vu2cpl/esp32-winkeyer/src/web.cpp

// ============================================================
//  VUKEYER — settings web server
//
//  Synchronous WebServer on port 80. Serviced from loop(), never
//  from the keyer task: serving the page takes a few ms of socket
//  work and element timing must not see it.
//
//  Routes:
//    GET  /              the settings console (one static page)
//    GET  /api/state     everything the page renders, as JSON
//    POST /api/set?k=..&v=..   one setting, via Settings::apply()
//    POST /api/send?t=..       queue text as CW
//    POST /api/tune?v=on|off   key down for tuning
//    GET  /api/flextrace       recent lines to/from the radio (?clear=1)
//    GET  /api/cwtable         radio CW timing per WPM; POST ?reset=1 forgets it
//    GET  /api/bt              Bluetooth keyboard detail + scan list
//    POST /api/bt?scan=1 | connect=<addr>&type=<n> | forget=1 | restart=1
//
//  Deliberately no authentication: this is shack-LAN kit on a
//  trusted VLAN, same posture as the WinKeyer TCP port next to it.
// ============================================================

#include "web.h"
#include "log.h"
#include "config.h"
#include "settings.h"
#include "keyer.h"
#include "fsk.h"
#include "memories.h"
#include "hostlink.h"
#include "flex.h"
#include "bt.h"
#include <WebServer.h>
#include <ESPmDNS.h>
#include <ArduinoJson.h>
#include <WiFi.h>

namespace {

WebServer server(80);
bool started = false;

// Styled after soft-MORCONI's console: dark chassis, amber panel labels,
// LED-style status dots. Fonts are system stacks, not Google Fonts — the
// keyer is often on a VLAN with no route to the internet, and a page that
// waits on fonts.googleapis.com would stall for every operator.
const char PAGE[] PROGMEM = R"HTML(<!DOCTYPE html>
<html lang="en"><head><meta charset="utf-8">
<meta name="viewport" content="width=device-width,initial-scale=1">
<title>VUKEYER — Settings</title><style>
:root{--chassis:#2d2d30;--dark:#1a1a1c;--bezel:#0a0a0b;--label:#d8cfb8;
--dim:#8a8275;--amber:#ffaa22;--green:#2aff5a;--red:#ff2a1a;--off:#3a1a18}
*{box-sizing:border-box}
body{margin:0;padding:8px;background:#0c0c0e radial-gradient(ellipse at top,#1a1a1c,#050505);
color:var(--label);font:14px/1.45 ui-monospace,Menlo,Consolas,monospace;min-height:100vh}
/* Panels tile into as many columns as the window allows, so the whole
   console fits one screen on a desktop and falls back to a single column
   on a phone. auto-fit + minmax does that without a breakpoint per size. */
.rig{max-width:1500px;margin:0 auto;padding:10px;border-radius:12px;
display:grid;grid-template-columns:1fr;
gap:6px 12px;align-items:start;
background:linear-gradient(180deg,#4a4a50 0%,#2d2d30 30%,#1f1f22 100%);
box-shadow:inset 0 2px 0 rgba(255,255,255,.18),inset 0 -3px 0 rgba(0,0,0,.7),0 24px 48px rgba(0,0,0,.7)}
/* Full-width furniture: the header, the lamps, a warning, the big speed
   readout and the footer read across the whole console, not per column. */
.rig>.brand,.rig>.leds,.rig>.slicewarn,.rig>.speed,.rig>.foot{grid-column:1/-1}
/* The backend panel carries the most rows; give it two columns when there
   is room, and let it collapse with everything else when there is not. */
/* Explicit breakpoints rather than auto-fit: auto-fit kept a ~800px window
   in ONE column, which stretched every slider across the full width and
   squeezed the memories into a single inner cell. */
@media(min-width:760px) {.rig{grid-template-columns:repeat(2,minmax(0,1fr))}}
@media(min-width:1150px){.rig{grid-template-columns:repeat(3,minmax(0,1fr))}}
@media(min-width:1680px){.rig{grid-template-columns:repeat(4,minmax(0,1fr))}}
@media(min-width:1150px){
  .wide{grid-column:span 2}
  /* BACKEND needs two columns; let a later card fill the hole it leaves. */
  .rig{grid-auto-flow:row dense}
  /* Lamps and the speed readout share one line instead of taking two. */
  .rig>.leds{grid-column:1/-2}
  .rig>.speed{grid-column:-2/-1;margin-bottom:0}
}
/* A slider does not get more useful past a few hundred pixels; without a
   cap a full-width card turns Speed into a metre of travel. */
input[type=range]{max-width:340px}
/* Memories and the backend panel share a grid row, as do USB / WIFI and
   FSK / RTTY below them; each pair is stretched to one height.
   Memories shares a grid row with the backend panel, which is much taller.
   .rig is align-items:start, so the card stopped at its content and the two
   ended at different heights. */
.stretch{align-self:stretch}
/* Every panel ends level with the ones it shares a row with. */
.rig>fieldset{align-self:stretch}
/* The six memories are wrapped in one div, so they were living in a single
   inner column. Give that div the full card and tile inside it. */
#mems{grid-column:1/-1;display:grid;
grid-template-columns:repeat(auto-fit,minmax(290px,1fr));gap:2px 12px}
.brand{display:flex;justify-content:space-between;align-items:baseline;
padding-bottom:8px;border-bottom:2px solid var(--bezel);margin-bottom:4px}
.brand b{font-size:19px;letter-spacing:3px;color:var(--amber);text-shadow:0 0 12px rgba(255,170,34,.5)}
.brand span{font-size:11px;color:var(--dim)}
/* no display rule here, so the hidden attribute still hides it */
.slicewarn{padding:9px 12px;margin:-6px 0 14px;border-radius:8px;font-size:13px;
background:rgba(255,170,34,.12);border:1px solid var(--amber);color:var(--amber)}
.leds{display:flex;gap:14px;flex-wrap:wrap;padding:8px 12px;margin-bottom:2px;
background:var(--bezel);border-radius:8px;font-size:11px;letter-spacing:1px}
.led{display:flex;align-items:center;gap:6px;color:var(--dim)}
.led i{width:9px;height:9px;border-radius:50%;background:var(--off);display:inline-block}
.led.on i{background:var(--green);box-shadow:0 0 8px var(--green)}
.led.warn i{background:var(--amber);box-shadow:0 0 8px var(--amber)}
.speed{background:var(--bezel);border-radius:8px;padding:8px 16px;margin-bottom:2px;
display:flex;align-items:baseline;gap:12px}
.speed b{font-size:34px;color:var(--amber);text-shadow:0 0 16px rgba(255,170,34,.45);line-height:1}
.speed span{color:var(--dim);font-size:12px;letter-spacing:2px}
fieldset{border:1px solid #44444a;border-radius:8px;margin:0;padding:6px 12px 9px;
min-width:0}   /* min-width:0 or a long row stretches its grid column */
/* Rows tile inside a panel too — a label plus one control is ~230px, so
   two or three sit side by side in a wide panel instead of stacking. */
fieldset{display:grid;grid-template-columns:repeat(auto-fit,minmax(196px,1fr));
gap:2px 14px;align-content:start}
fieldset>legend{grid-column:1/-1}
/* A merged card keeps its old panels as sections under a small heading. */
.sub{grid-column:1/-1;margin:8px 0 0;padding-top:6px;border-top:1px dashed #44444a;
color:var(--amber);font-size:10px;letter-spacing:2px;opacity:.8}
.sub.first{margin-top:0;padding-top:0;border-top:0}
.sub[title]{cursor:help}
/* Anything with a slider, a free-text field or its own buttons wants the
   full width of its panel; :has covers the sliders without marking each. */
.row.full,.row:has(input[type=range]),.row:has(input[type=text]):not(.mem){grid-column:1/-1}

legend{color:var(--amber);font-size:11px;letter-spacing:2px;padding:0 6px}
.row{display:flex;align-items:center;gap:9px;margin:4px 0;flex-wrap:wrap}
/* An author rule beats the hidden attribute's default display:none, so
   .row{display:flex} kept "hidden" rows on screen. */
.row[hidden]{display:none!important}
/* Closed, it is one tile beside Radio and Keying; open, it takes the width. */
details.adv{margin:4px 0;align-self:center}
details.adv[open]{grid-column:1/-1;margin-top:6px;border-top:1px dashed #44444a;padding-top:4px}
details.adv[hidden]{display:none!important}
details.adv summary{cursor:pointer;color:var(--dim);font-size:12px}
.advwarn{margin:6px 0;padding:6px 9px;border-radius:6px;font-size:12px;
background:rgba(255,170,34,.12);border:1px solid var(--amber);color:var(--amber)}
.row label{flex:0 0 92px;color:var(--dim);font-size:12px}
input,select,button{font:inherit;background:#131315;color:var(--label);
border:1px solid #44444a;border-radius:5px;padding:3px 8px;font-size:13px}
input[type=range]{flex:1;min-width:150px;padding:0;border:none;background:none;
-webkit-appearance:none;appearance:none;height:18px}
input[type=range]::-webkit-slider-runnable-track{height:5px;border-radius:3px;
background:#131315;box-shadow:inset 0 1px 2px rgba(0,0,0,.9)}
input[type=range]::-moz-range-track{height:5px;border-radius:3px;background:#131315}
input[type=range]::-webkit-slider-thumb{-webkit-appearance:none;appearance:none;
width:15px;height:15px;margin-top:-5px;border-radius:50%;border:1px solid #1a1a1c;
background:linear-gradient(180deg,#d8cfb8,#8a8275);box-shadow:0 0 7px rgba(255,170,34,.55)}
input[type=range]::-moz-range-thumb{width:15px;height:15px;border-radius:50%;
border:1px solid #1a1a1c;background:linear-gradient(180deg,#d8cfb8,#8a8275)}
input[type=checkbox]{accent-color:var(--amber)}
input[type=text]{width:92px}
/* Wide enough for "2000" and the spinner, narrow enough that label + field
   + unit clears a half-width panel column with room to spare. */
input[type=number]{width:78px}
button{cursor:pointer;background:linear-gradient(180deg,#44444a,#26262a);
letter-spacing:.5px;padding:3px 9px;font-size:12px}
button:hover{border-color:var(--amber);color:var(--amber)}
button.hot{color:var(--red);border-color:#5a2420}
.val{color:var(--amber);min-width:56px;font-size:13px}
/* A fixed unit ("ms", "WPM") is not a readout: reserving 56px for it was
   enough to push it onto a second line inside a half-width panel column.
   .val keeps its width because a CHANGING value there would resize the
   slider beside it on every drag. */
.unit{color:var(--amber);font-size:13px;white-space:nowrap}
/* A <select> is as wide as its longest option and will not shrink below
   it, so "1200 8N2 - ... standard" hung out past the panel border. */
select{max-width:100%}
/* Memories: six rows that must each stay on ONE line, or the panel becomes
   the tallest thing on the page and nothing else fits beside it. */
.row.mem{margin:3px 0;gap:6px}
.row.mem button{padding:4px 7px;font-size:11px;letter-spacing:0}
.row label[title]{border-bottom:1px dotted var(--dim);cursor:help}
legend[title]{cursor:help}
#msg{min-height:16px;font-size:12px;color:var(--green);margin-top:4px}
#msg.err{color:var(--red)}
.foot{margin-top:4px;font-size:11px;color:var(--dim);text-align:center}
</style></head><body><div class="rig">
<div class="brand"><b>VUKEYER</b><span>VU2CPL &middot; ESP32</span></div>

<div class="leds">
<div class="led" id="l-host"><i></i>HOST</div>
<div class="led" id="l-tcp"><i></i>TCP</div>
<div class="led" id="l-key"><i></i>KEY</div>
<div class="led" id="l-tune"><i></i>TUNE</div>
<div class="led" id="l-pot"><i></i>POT</div>
<div class="led" id="l-flex"><i></i>FLEX</div>
<div class="led" id="l-disp"><i></i>OLED</div>
<div class="led" id="l-kbd"><i></i>KBD</div>
</div>
<div class="slicewarn" id="slicewarn" hidden></div>
<div class="slicewarn" id="practicewarn" hidden>PRACTICE &mdash; sidetone only, nothing is transmitted</div>

<div class="speed"><b id="wpmBig">--</b><span>WPM</span><span id="src"></span></div>

<fieldset><legend>KEYER</legend>
<div class="row"><label title="Sidetone only: paddle, memories, typed text, a logger's text and TUNE all sound in your ear, but no KEY or PTT line is driven, nothing is sent to the radio, and RTTY is refused. Turning it on or off stops whatever is being sent. Not saved: the keyer always boots ready to transmit.">Practice</label>
  <label style="flex:0 0 auto"><input type="checkbox" id="practice"> sidetone only, no TX</label></div>
<div class="row"><label title="Sending speed in words per minute (PARIS timing: dit = 1200/WPM ms). A logger or the speed pot can override this; only what you set here is saved.">Speed</label>
  <input type="range" id="wpm" min="5" max="60"><span class="val" id="wpmV"></span></div>
<div class="row"><label title="Echo of characters you send on the PADDLE, so a logger can capture hand-sent text. This is mode register bit 6 of the logger protocol, separate from character echo of buffered text. Auto follows what the host asks for — but RUMlogNG sets 0x07 and never requests it, so force it On if you want hand-sent text logged.">Paddle echo</label>
  <select id="pecho"><option value="auto">Auto (follow host)</option>
  <option value="on">On</option><option value="off">Off</option></select>
  <span class="val" id="pechoState"></span></div>
<div class="row"><label title="Iambic A releases both paddles to stop after the current element; iambic B sends one more. Swap exchanges dit and dah if the paddle is wired the other way round.">Mode</label>
  <select id="mode"><option value="a">Iambic A</option><option value="b">Iambic B</option></select>
  <label style="flex:0 0 auto"><input type="checkbox" id="swap"> swap paddles</label></div>
<div class="row"><label title="Monitor tone pitch in Hz, 300-1000, default 600. Local only — it never reaches the air. A logger can ask for another pitch over the host link (the command sends 4000/N); that lasts its session and is clamped to this range.">Sidetone</label>
  <input type="range" id="sthz" min="300" max="1000" step="10"><span class="val" id="sthzV"></span></div>
<div class="sub">TIMING</div>
<div class="row"><label title="Mark/space balance, 10-90, nominal 50. Higher makes elements longer and gaps shorter WITHOUT changing the WPM. Raise it a little if your fist sounds clipped on the air.">Weight</label>
  <input type="range" id="weight" min="10" max="90"><span class="val" id="weightV"></span></div>
<div class="row"><label title="Dah length relative to a dit, 33-66, nominal 50 = the standard 3 dits. Away from 50 the CW stops being standard-weight, so move it only to match a fist you already like.">Dah ratio</label>
  <input type="range" id="ratio" min="33" max="66"><span class="val" id="ratioV"></span></div>
<div class="row"><label title="0 = off. Otherwise characters stay at the Speed above while the GAPS stretch to this slower WPM — the standard way to learn at speed. Must be 0 or 5-60; 1-4 is not a legal value.">Farnsworth</label>
  <input type="number" id="farns" min="0" max="60"><span class="unit">WPM</span></div>
<div class="sub">SPEED POT</div>
<div class="row"><label title="10k linear pot on GPIO34, wiper to the pin, 100nF to GND. Leave this OFF until one is actually wired: the pin floats and noise will drive your speed. The knob overrides a host-set speed the moment you turn it.">Knob</label>
  <label style="flex:0 0 auto"><input type="checkbox" id="pot"> enabled</label></div>
<div class="row full"><label title="WPM at each end of the knob travel. Expect a small dead zone at the top: the ESP32 ADC saturates near 3.1 V rather than 3.3 V.">Range</label>
  <input type="number" id="potmin" min="5" max="59"><span class="unit">to</span>
  <input type="number" id="potmax" min="6" max="60"><span class="unit">WPM</span></div>
<div class="sub" id="legPtt" title="">PTT</div>
<div class="row"><label title="The PTT line itself: GPIO32, and GPIO19 for radio 2. Unticked, PTT is never asserted at all. It stays live on both backends, for an amp or a sequencer.">PTT line</label>
  <label style="flex:0 0 auto"><input type="checkbox" id="ptt"> enabled</label></div>
<div class="row"><label title="Master on/off for the tone in your ear, from the piezo on GPIO4. Off means silence regardless of anything else.">Audio</label>
  <label style="flex:0 0 auto"><input type="checkbox" id="st"> sidetone</label></div>
<div class="row"><label title="Delay in ms between asserting PTT and the first element, so a relay or amp has time to switch. Applies to the local GPIO32 line; the Flex radio does its own T/R.">Lead-in</label>
  <input type="number" id="lead" min="0" max="2000"><span class="unit">ms</span></div>
<div class="row"><label title="How long PTT is held after the last element, in ms. Releases BOTH the local line and, on the Flex backend, the radio. A useful reference: one word gap is 7 dits = 8400/WPM ms, so 400 ms is exactly one word space at 21 WPM.">Tail</label>
  <input type="number" id="tail" min="0" max="2000"><span class="unit">ms</span></div>
</fieldset>

<fieldset><legend title="Six canned messages kept in flash, played through whichever backend is current. %C in the text expands to your callsign, so a memory survives a contest call change. No GPIO cost — front-panel buttons can be wired to these later.">MEMORIES</legend>
<div class="row"><label title="Expands wherever %C appears in a memory.">Callsign</label>
  <input type="text" id="call" style="width:120px" placeholder="VU2CPL"></div>
<div id="mems"></div>
<div class="sub" title="Type text and press Enter or SEND to transmit it. The SEND button turns into STOP while anything is going out — a message, a memory or tune — and ends it, clearing the radio's buffer as well as the keyer's. TUNE keys continuously for tuning an amp. Number boxes on this page step with the arrow keys, Shift for 10.">SEND</div>
<div class="row"><input type="text" id="txt" style="flex:1;width:auto" placeholder="CQ TEST VU2CPL">
  <button id="sendBtn" onclick="sendOrStop()">SEND</button>
  <button id="tuneBtn" onclick="tuneOrStop()">TUNE</button></div>
<div id="msg"></div>
<div class="sub" title="RTTY FSK keying line on GPIO27: Baudot at 45.45 baud, 1 start bit, 5 data bits, 1.5 stop bits, mark when idle. Invert if your rig wants mark low — wrong polarity prints as reversed-case gibberish at the far end rather than silence. Diddle sends LTRS while the transmitter is up with nothing to say, keeping the far end synchronised between overs. PTT is held for the whole over, not per character.">FSK / RTTY</div>
<div class="row"><input type="text" id="fsktxt" style="flex:1;width:auto" placeholder="RYRYRY DE VU2CPL">
  <button id="fskBtn" onclick="fskSendOrStop()">SEND</button></div>
<div class="row full"><label title="45.45 baud is standard amateur RTTY. 75 is used on some commercial circuits.">Baud</label>
  <select id="fskbaud"><option value="45.45">45.45 (standard)</option>
  <option value="50">50</option><option value="75">75</option></select>
  <span class="val" id="fskState"></span></div>
<!-- The two switches get their own row: a label, a select and two checkboxes
     on one line overflow this panel at every window width, and the leftover
     checkbox wrapping alone underneath is the ugliest way to lose that fight.
     The spacer keeps them lined up with the controls above. -->
<div class="row full"><span style="flex:0 0 92px"></span>
  <label style="flex:0 0 auto"><input type="checkbox" id="fskinv"> invert</label>
  <label style="flex:0 0 auto"><input type="checkbox" id="fskdid"> diddle</label></div>
</fieldset>

<fieldset class="wide stretch"><legend>BACKEND</legend>
<div class="row"><label title="Enable the FlexRadio backend: discovery, connection and keying over the network. Harmless with no radio present — it simply listens for a discovery broadcast that never arrives. Separate from Keying below, which decides where your CW actually goes.">FlexRadio</label>
  <label style="flex:0 0 auto"><input type="checkbox" id="flex"> enabled</label>
  <span class="val" id="flexState"></span></div>
<div class="row flexonly"><label title="Pin the radio's address. Discovery is a raw UDP broadcast and does not cross subnets or VLANs, so if the radio is on a different segment from the keyer it will never be found automatically — use Find radio below. Leave blank to use discovery.">Radio IP</label>
  <input type="text" id="flexip" style="width:130px" placeholder="auto (discovery)"></div>
<div class="row flexonly"><label title="Discovery only hears a radio on the keyer's own subnet — it listens for a UDP broadcast, and routers do not pass those between subnets or VLANs. SCAN tries every address in one /24 for the radio's API port (TCP 4992) instead, which does cross a router, and lists what answers; click one to use it. Leave the box blank to scan the keyer's own subnet, or type the first three numbers of the radio's (e.g. 192.168.1). Takes about 15 seconds. Read-only: it asks each radio what it is and disconnects.">Find radio</label>
  <input type="text" id="scannet" style="width:130px">
  <button onclick="scan()">SCAN</button>
  <span class="val" id="scanState"></span>
  <span id="scanHits"></span></div>
<div class="row flexonly"><label title="The radio starts sending a few hundred ms after it is handed the text — network, then its own CW start — while the local sidetone copy starts at once, so the sidetone runs AHEAD of the air. This holds the copy back to match. Auto uses the delay the keyer measures from cwx send to the radio actually transmitting; set a number to override, 0 to disable.">Sidetone delay</label>
  <input type="number" id="mondelay" min="0" max="2000" placeholder="auto">
  <label style="flex:0 0 auto"><input type="checkbox" id="mondelayauto"> auto</label>
  <span class="val" id="mondelayNow"></span></div>
<div class="row flexonly"><label title="Added to the measured delay while auto is ticked; ignored for a manual value. Auto lines the sidetone up with the radio, but a client that plays the radio's sidetone back as audio (AetherSDR, SmartSDR) adds its own network and audio delay that the keyer cannot measure. Tune by ear: AetherSDR needed about 140-160.">Delay extra</label>
  <input type="number" id="monextra" min="0" max="1000"><span class="unit">ms</span></div>
<div class="row flexonly"><label title="The radio generates buffered CW itself via cwx send, so this keyer produces no elements and no sound while the rig transmits. Monitor runs a second copy of that text through the local keyer purely to make sidetone, so you can hear what is going out. Needs Audio/sidetone on as well. Does nothing on the local backend, where the keyer makes the elements itself.">Monitor</label>
  <label style="flex:0 0 auto"><input type="checkbox" id="monitor"> sound what the radio sends</label></div>
<div class="row"><label title="Which KEY/PTT pair the keyer drives. Radio 1 is GPIO33/32, radio 2 is GPIO18/19. Both keys them together — intended for a rig plus an amp or monitor, but it does mean two transmitters key at once.">Radio</label>
  <select id="radio"><option value="1">Radio 1</option>
  <option value="2">Radio 2</option><option value="both">Both</option></select></div>
<div class="row"><label title="Local keys the wire: KEY on GPIO33, PTT on GPIO32. FlexRadio keys the radio over the network instead and leaves GPIO33 idle so the rig is not keyed twice — it needs a slice in use and in CW mode or the radio transmits nothing and reports no error.">Keying</label>
  <select id="backend"><option value="local">Local key line</option>
  <option value="flex">FlexRadio (network)</option></select>
  <span class="val" id="flexip"></span></div>
<details class="adv flexonly"><summary>Advanced keying</summary>
<div class="advwarn">These change how the paddle keys the radio. A wrong value can leave the radio silent (0 W) with no error shown. The working set is cw key, bind GUI off, xmit on &mdash; DEFAULTS puts it back.</div>
<div class="row"><label title="Which command sends each paddle element to the radio. 'cw key' transmits. 'cw ptt' is what FlexRadio's wiki documents, but the radio accepts it and produces no RF (found with a power meter). Default: cw key.">Key verb</label>
  <select id="flexcmd"><option value="key">cw key</option><option value="ptt">cw ptt</option></select>
  <label style="flex:0 0 auto" title="Send 'client bind' to the GUI client (SmartSDR, Maestro, AetherSDR). Off by default: binding wedged the radio's CW generator, so CW went out at 0 W after a GUI client restarted. The keyer follows the GUI client without it."><input type="checkbox" id="flexbind"> bind GUI</label>
  <label style="flex:0 0 auto" title="Take the transmitter with 'xmit 1' before paddle keying and release it with 'xmit 0' after the tail. The radio only keys for the client that holds the transmitter, so paddle keying needs this on. Memories and typed text are not affected. Default: on."><input type="checkbox" id="flexxmit"> xmit</label>
  <button onclick="flexDefaults()">DEFAULTS</button></div>
</details>
</fieldset>

<fieldset><legend>SYSTEM</legend><div class="sub first">DISPLAY</div>
<div class="row"><label title="Any I2C panel on 21/22, probed at boot. The FAMILY is auto-detected — OLEDs answer at 0x3C/0x3D, HD44780 LCD backpacks at 0x27/0x3F — so one firmware runs whichever is plugged in, and Auto-detect gets you back to the OLED after trying an LCD. What cannot be detected: SH1106 vs SSD1306 (same address; wrong choice shifts the image 2px right with a garbage left edge) and 16x2 vs 20x4 (same chip; wrong choice just truncates). Run /i2c to scan the bus.">Panel</label>
  <label style="flex:0 0 auto"><input type="checkbox" id="disp"> enabled</label>
  <select id="dispctl">
    <option value="auto">Auto-detect</option>
    <option value="sh1106">OLED SH1106 (1.3")</option>
    <option value="ssd1306">OLED SSD1306 (0.96")</option>
    <option value="lcd20x4">LCD 20x4 (I&sup2;C)</option>
    <option value="lcd16x2">LCD 16x2 (I&sup2;C)</option>
  </select></div>
<div class="sub" id="legSerial" title="">USB / WIFI</div>
<div class="row full"><label title="WiFi transmit power. Lower draws less current in each transmit burst, which is what browns out a board on a marginal USB supply — paddle keying sends a packet per key edge, about twenty bursts a second, and this board reset within two characters at full power. Lower also means less range: it does not affect how well you hear the AP, only how well it hears you. 11 dBm was enough to stop the resets here. The real fix is a 470-1000uF capacitor across 3V3 at the board, after which full power can come back.">WiFi power</label>
  <select id="txpower">
    <option value="19">19 dBm (full)</option>
    <option value="17">17 dBm</option>
    <option value="15">15 dBm</option>
    <option value="13">13 dBm</option>
    <option value="11">11 dBm (low draw)</option>
    <option value="8">8 dBm</option>
    <option value="5">5 dBm</option>
    <option value="2">2 dBm (minimum)</option>
  </select>
  <span class="val" id="rssiVal"></span></div>
<div class="row full"><label title="1200 8N2 is the standard rate and what loggers open the port with — at any other rate the handshake arrives as noise and the keyer looks dead. The console shares this port, so at 1200 the boot log is trimmed to one line. This page is unaffected by the serial rate, so it is the way back if you pick a rate you cannot monitor at.">Host baud</label>
  <select id="baud">
    <option value="1200">1200 8N2 &mdash; loggers</option>
    <option value="9600">9600 8N1</option>
    <option value="19200">19200 8N1</option>
    <option value="38400">38400 8N1</option>
    <option value="57600">57600 8N1</option>
    <option value="115200">115200 8N1 &mdash; console</option>
  </select></div>
<div class="sub" title="Type CW on a Bluetooth LE keyboard. Letters, digits and punctuation go out as you type; F1-F6 play the memories (hold Fn if the top row is media keys); Esc stops everything; PgUp/PgDn or the arrow keys change speed. BLE only: a keyboard that speaks only Classic Bluetooth will not show up.">BT KEYBOARD</div>
<div class="row full"><label title="Off by default, and changing it takes a restart. While Bluetooth runs, ESP-IDF forces WiFi modem sleep on, which measured about 85 ms average latency with spikes past 200 ms — typed text does not mind, but listen to your paddle through the Flex before relying on it. Off costs nothing: the Bluetooth memory is not even kept.">Bluetooth</label>
  <label style="flex:0 0 auto"><input type="checkbox" id="bt"> enabled</label>
  <span class="val" id="btState"></span>
  <button id="btRestart" onclick="btRestart()" hidden>RESTART</button></div>
<div class="row full btonly"><label title="Only one keyboard is kept; pairing another replaces it. A paired keyboard reconnects by itself when it wakes — press a key.">Keyboard</label>
  <span class="val" id="btName"></span>
  <button id="btForget" onclick="btForget()">FORGET</button></div>
<div class="row full btonly"><label title="Put the keyboard in Bluetooth pairing mode first (not its USB-dongle mode), then SCAN. It takes 10 seconds; click the keyboard in the list to pair.">Pair</label>
  <button onclick="btScan()">SCAN</button>
  <span class="val" id="btScanState"></span>
  <span id="btHits"></span></div>
<div class="row full" id="btPass" hidden style="font-size:20px;color:var(--amber);letter-spacing:2px"></div>
</fieldset>

<div class="foot" id="foot">vukeyer.local &middot; settings persist in NVS</div>
</div><script>
const $=i=>document.getElementById(i);
let editing=null,pend=null;
// Held so it can be put back once Flex is enabled again.
const flexOpt=document.querySelector('#backend option[value="flex"]');
function note(t,err){const m=$('msg');m.textContent=t;m.className=err?'err':''}
async function post(u){const r=await fetch(u,{method:'POST'});const t=await r.text();
  note(t,!r.ok);refresh()}
const KEYMAP={fskbaud:'fskbaud',fskinv:'fskinv',fskdid:'fskdiddle',
              flexbind:'flexbind',flexxmit:'flexxmit',flexcmd:'flexcmd'};
function set(k,v){post('/api/set?k='+(KEYMAP[k]||k)+'&v='+encodeURIComponent(v))}
// Back to the combination verified on air: cw key, no bind, xmit on.
async function flexDefaults(){
  await post('/api/set?k=flexcmd&v=key');
  await post('/api/set?k=flexbind&v=off');
  await post('/api/set?k=flexxmit&v=on');
  note('advanced keying back to defaults: cw key, bind GUI off, xmit on',false)}
function send(){const t=$('txt').value.trim();if(!t)return;
  post('/api/send?t='+encodeURIComponent(t));$('txt').value='';setBtn('sendBtn',true)}
function fsksend(){const t=$('fsktxt').value.trim();if(!t)return;
  post('/api/fsk?t='+encodeURIComponent(t));$('fsktxt').value='';setBtn('fskBtn',true)}
// SEND and STOP are the same button: a second one sitting there armed is
// only useful while something is transmitting, and a STOP that does nothing
// the rest of the time invites a click that clears a buffer mid-contest.
// The state comes from the poll; the click flips it at once so the button
// does not sit on SEND for up to a second while the message is going out.
function setBtn(id,on){const b=$(id);if(!b)return;
  b.textContent=on?'STOP':'SEND';b.classList.toggle('hot',on)}
function stopping(id){return $(id).classList.contains('hot')}
function sendOrStop(){
  if(stopping('sendBtn')){post('/api/send?stop=1');setBtn('sendBtn',false);return}
  send()}
function fskSendOrStop(){
  if(stopping('fskBtn')){post('/api/fsk?stop=1');setBtn('fskBtn',false);return}
  fsksend()}
function memPlay(n){post('/api/mem?play='+n);setMemBtn(n)}
// The STOP for a memory belongs on that memory's own row, not on the text
// SEND button: they are different things to stop, and a STOP on the row you
// did not press is a click nobody makes with confidence.
function setMemBtn(active){for(let n=1;n<=6;n++){const b=$('p'+n);if(!b)continue;
  const on=(n===active);b.textContent=on?'STOP':'PLAY';b.classList.toggle('hot',on)}}
function memPlayOrStop(n){
  if(stopping('p'+n)){post('/api/send?stop=1');setMemBtn(0);return}
  memPlay(n)}
function tuneOrStop(){
  if(stopping('tuneBtn')){post('/api/tune?v=off');setTuneBtn(false);return}
  post('/api/tune?v=on');setTuneBtn(true)}
function setTuneBtn(on){const b=$('tuneBtn');
  b.textContent=on?'STOP':'TUNE';b.classList.toggle('hot',on)}
function memSave(n){post('/api/mem?n='+n+'&t='+encodeURIComponent($('m'+n).value))}
let memsBuilt=false;
function buildMems(list){
  if(memsBuilt)return; memsBuilt=true;
  // NB: the returned string starts on the same line as `return` — a line
  // break there and automatic semicolon insertion silently returns undefined.
  $('mems').innerHTML=list.map((t,i)=>{const n=i+1;
    return '<div class="row mem"><label style="flex:0 0 24px">F'+n+'</label>'
      +'<input type="text" id="m'+n+'" style="flex:1;width:auto;min-width:0">'
      +'<button onclick="memSave('+n+')">SAVE</button>'
      +'<button id="p'+n+'" onclick="memPlayOrStop('+n+')">PLAY</button></div>';}).join('');
  list.forEach((t,i)=>$('m'+(i+1)).value=t);
}
function esc(t){return String(t).replace(/[&<>"']/g,c=>'&#'+c.charCodeAt(0)+';')}
async function scan(){
  const r=await fetch('/api/flexscan?net='+encodeURIComponent($('scannet').value.trim()),{method:'POST'});
  note(await r.text(),!r.ok); if(r.ok) pollScan();
}
async function pollScan(){
  let j;try{j=await(await fetch('/api/flexscan')).json()}catch(e){setTimeout(pollScan,1000);return}
  $('scanState').textContent=j.running?('scanning '+j.net+'.x \u2014 '+j.tried+'/254')
    :j.err?('stopped: '+j.err):j.hits.length?'':'no radio on '+j.net+'.x';
  $('scanHits').innerHTML=j.hits.map(h=>'<button onclick="useRadio(\''+esc(h.ip)+'\')">'
    +esc(h.ip)+(h.model?' &middot; '+esc(h.model):'')+(h.name?' &middot; '+esc(h.name):'')
    +'</button>').join(' ');
  if(j.running) setTimeout(pollScan,700);
}
function useRadio(ip){$('flexip').value=ip;set('flexip',ip);note('radio IP set to '+ip)}
// Bluetooth keyboard. Like the radio finder, the device list is polled only
// while a scan runs; the rest of the card comes from /api/state.
async function btScan(){
  const r=await fetch('/api/bt?scan=1',{method:'POST'});
  note(await r.text(),!r.ok); if(r.ok) pollBt();
}
async function pollBt(){
  let j;try{j=await(await fetch('/api/bt')).json()}catch(e){setTimeout(pollBt,1000);return}
  $('btScanState').textContent=j.scanning?'scanning…'
    :j.hits.length?'':'nothing found — is it in Bluetooth pairing mode?';
  $('btHits').innerHTML=j.hits.map(h=>'<button onclick="btConnect(\''+esc(h.addr)+'\','+(h.type|0)+')">'
    +esc(h.name||h.addr)+' &middot; '+h.rssi+' dBm'+(h.paired?' &middot; paired':'')+'</button>').join(' ');
  if(j.scanning) setTimeout(pollBt,700);
}
function btConnect(a,t){post('/api/bt?connect='+encodeURIComponent(a)+'&type='+t)}
function btForget(){post('/api/bt?forget=1')}
function btRestart(){post('/api/bt?restart=1')}
function led(id,on,warn){const e=$(id);e.className='led'+(on?(warn?' warn':' on'):'')}
async function refresh(){
  let s;try{s=await(await fetch('/api/state')).json()}catch(e){return}
  $('wpmBig').textContent=s.wpm;
  $('src').textContent=s.pot?'FROM KNOB':'HOST/WEB SET';
  led('l-host',s.host);led('l-tcp',s.tcp);led('l-key',s.key);
  led('l-tune',s.tune,true);led('l-pot',s.pot);
  led('l-flex',s.flex.enabled&&s.flex.connected,s.flex.enabled&&!s.flex.slice);
  led('l-disp',s.disp&&s.disphw);
  {
    const b=s.bt||{};
    // led() only honours "warn" on a lit lamp: green = typing, amber = BT up
    // but no keyboard, dark = off.
    led('l-kbd',!!b.on,b.st!=='connected');
    $('bt').checked=!!b.en;
    // RESTART only when the saved switch and the running stack disagree.
    $('btRestart').hidden=(!!b.en===!!b.on)||b.st==='unsupported';
    $('btState').textContent=b.st==='unsupported'?'not in this build'
      :(!b.en&&b.err)?'switched off at boot — only '+Math.round(b.err/1024)+' KB free with Bluetooth'
      :(!!b.en!==!!b.on)?'restart to '+(b.en?'start':'stop')
      :b.on?b.st:'off';
    for(const el of document.querySelectorAll('.btonly')) el.hidden=!b.on;
    $('btName').textContent=b.name?(b.name+(b.batt>=0?' · battery '+b.batt+'%':'')):'none paired';
    $('btForget').hidden=!b.name;
    const pk=(b.pk|0)>=0;
    $('btPass').hidden=!pk;
    if(pk) $('btPass').textContent='Type '+String(b.pk).padStart(6,'0')+' on the keyboard, then Enter';
  }
  const w=s.flex.slicewarn||'';
  $('slicewarn').textContent='⚠ '+w; $('slicewarn').hidden=!w;
  $('practice').checked=!!s.practice; $('practicewarn').hidden=!s.practice;
  $('flexState').textContent = !s.flex.enabled ? 'off'
      : s.flex.connected ? (s.flex.slice ? 'ready' : 'no CW slice')
      : 'searching';
  $('flex').checked=s.flex.enabled;
  // Gated on the ENABLE. The detail rows go when Flex is off, and the
  // Keying selector stops offering Flex at all — so there is no way to
  // select a backend that is not enabled, and no lockout either, because
  // the enable checkbox itself always stays on screen.
  for (const el of document.querySelectorAll('.flexonly'))
    el.hidden = !s.flex.enabled;
  // Safari ignores hidden/disabled on <option> — it still lists them — so
  // the entry has to leave the DOM entirely. Kept if it is the CURRENT
  // value, otherwise the select would go blank and hide the real state.
  const sel = $('backend');
  if (s.flex.enabled) {
    if (!flexOpt.parentNode) sel.appendChild(flexOpt);
  } else if (flexOpt.parentNode) {
    flexOpt.remove();      // the firmware has already moved keying to local
  }
  $('flexbind').checked=s.flex.bind; $('flexxmit').checked=s.flex.xmit;
  if(editing!=='flexip') $('flexip').value=s.flex.ip||'';
  if(s.ip) $('scannet').placeholder=s.ip.split('.').slice(0,3).join('.');
  {
    const u = s.uptime|0;
    const t = u < 90 ? u + 's' : u < 5400 ? Math.round(u/60) + 'm'
                                          : (u/3600).toFixed(1) + 'h';
    $('foot').textContent = 'vukeyer.local \u00b7 up ' + t
      + ' \u00b7 last reset: ' + (s.resetreason || '?');
  }
  $('legSerial').title = s.baud==1200
    ? 'Ready for a logger: 1200 8N2 is what loggers expect.'
    : 'Console rate. A logger will NOT talk to the port '
      +'at this setting.';
  $('legPtt').title = s.backend==='flex'
    ? 'FlexRadio backend: Tail releases both the local PTT line and the radio '
      +'(xmit 0). Lead-in drives GPIO32 only — still live for an amp — since '
      +'the radio does its own T/R. KEY on GPIO33 is idle.'
    : 'Local backend: lead-in and tail sequence PTT on GPIO32 around the KEY '
      +'line on GPIO33.';
  const fill={wpm:s.wpm,sthz:s.sthz,mode:s.mode,potmin:s.potmin,potmax:s.potmax,
    backend:s.backend,dispctl:s.dispctl,baud:String(s.baud),
    txpower:String(s.txpower),
    pecho:(s.pecho==2?'auto':(s.pecho==1?'on':'off')),
    // The board sends a float, so 45.45 arrives as 45.45000076 and matches
    // no <option value>, leaving the select blank. Round to hundredths.
    fskbaud:String(Math.round(s.fskbaud*100)/100),radio:(s.radio==3?'both':String(s.radio)),
    flexcmd:s.flex.cmd,
    weight:s.weight,ratio:s.ratio,
    farns:s.farns,lead:s.lead,tail:s.tail};
  for(const k in fill) if(editing!==k) $(k).value=fill[k];
  $('swap').checked=s.swap;$('pot').checked=s.pot;$('disp').checked=s.disp;
  $('ptt').checked=s.ptt;$('st').checked=s.st;$('monitor').checked=s.monitor;
  {const auto_=s.mondelay<0; $('mondelayauto').checked=auto_;
   $('mondelay').disabled=auto_;
   if(editing!=='mondelay') $('mondelay').value=auto_?'':s.mondelay;
   $('monextra').disabled=!auto_;
   if(editing!=='monextra') $('monextra').value=s.monextra||0;
   $('mondelayNow').textContent=(s.mondelaynow||0)+' ms'+
     (auto_?' (auto '+(s.flexlatency||0)+')':'');}
  $('pechoState').textContent = s.pechoon ? 'active' : 'inactive';
  $('rssiVal').textContent = s.rssi + ' dBm rx';
  buildMems(s.mems||[]);
  if(editing!=='call') $('call').value=s.call||'';
  $('fskinv').checked=s.fskinv; $('fskdid').checked=s.fskdid;
  $('fskState').textContent = s.fskbusy ? 'SENDING' : '';
  // Each button ends what it started, so only one STOP is ever on screen:
  // tune has its own, a memory's lives on its row, and SEND keeps the rest.
  setTuneBtn(!!s.tune);
  setMemBtn(s.memplay||0);
  setBtn('sendBtn', !!(s.busy && !s.tune && !s.memplay));
  setBtn('fskBtn',  !!s.fskbusy);
  $('wpmV').textContent=$('wpm').value+' WPM';
  $('sthzV').textContent=$('sthz').value+' Hz';
  $('weightV').textContent=$('weight').value+(s.weight==50?' (nominal)':'');
  $('ratioV').textContent=$('ratio').value+(s.ratio==50?' (nominal)':'');
}
// Sliders: track the label live, but only write on release — one NVS
// commit per drag instead of one per pixel.
for(const [id,lbl,suf] of [['wpm','wpmV',' WPM'],['sthz','sthzV',' Hz'],
                           ['weight','weightV',''],['ratio','ratioV','']]){
  $(id).oninput=e=>{editing=id;$(lbl).textContent=e.target.value+suf};
  $(id).onchange=e=>{editing=null;set(id,e.target.value)};
}
// Number boxes. Two things make these painful without help: the 1 Hz poll
// overwrites whatever you are part-way through entering, and every keypress
// would otherwise be its own POST and its own NVS write. So: claim the field
// while it has focus, and debounce the write so holding an arrow key costs
// one commit at the end rather than one per repeat.
function bindNum(id,min,max){
  const e=$(id);
  e.onfocus=()=>editing=id;
  e.onblur =()=>{editing=null;clearTimeout(pend);set(id,e.value)};
  e.oninput=()=>{editing=id;clearTimeout(pend);pend=setTimeout(()=>set(id,e.value),500)};
  e.onkeydown=ev=>{
    if(ev.key==='Enter'){clearTimeout(pend);set(id,e.value);e.blur();return}
    if(ev.key!=='ArrowUp'&&ev.key!=='ArrowDown')return;
    ev.preventDefault();                       // step ourselves so it clamps
    const d=(ev.shiftKey?10:1)*(ev.key==='ArrowUp'?1:-1);
    e.value=Math.max(min,Math.min(max,(parseInt(e.value,10)||0)+d));
    editing=id; clearTimeout(pend);
    pend=setTimeout(()=>set(id,e.value),400);
  };
}
bindNum('farns',0,60); bindNum('lead',0,2000); bindNum('tail',0,2000);
bindNum('mondelay',0,2000); bindNum('monextra',0,1000);
// The tickbox is the mode; the box is the manual value it falls back to.
$('mondelayauto').onchange=e=>set('mondelay',
  e.target.checked ? 'auto' : ($('mondelay').value||'0'));
bindNum('potmin',5,59); bindNum('potmax',6,60);
$('call').onfocus=()=>editing='call';
$('call').onblur =()=>{editing=null;post('/api/mem?call='+encodeURIComponent($('call').value))};
$('flexip').onfocus=()=>editing='flexip';
$('flexip').onblur =()=>{editing=null;set('flexip',$('flexip').value)};
for(const id of ['mode','backend','dispctl','baud','pecho','fskbaud','radio','flexcmd','txpower'])
  $(id).onchange=e=>set(id,e.target.value);
for(const id of ['swap','pot','disp','ptt','st','monitor','practice','fskinv','fskdid',
                 'flex','flexbind','flexxmit','bt'])
  $(id).onchange=e=>set(id,e.target.checked?'on':'off');
$('txt').addEventListener('keydown',e=>{if(e.key==='Enter')send()});
$('fsktxt').addEventListener('keydown',e=>{if(e.key==='Enter')fsksend()});
refresh();setInterval(refresh,1000);
</script></body></html>)HTML";

void handleState() {
  // Heap, NOT the stack. This began as StaticJsonDocument<640> and grew to
  // 2560 as fields were added — 2.5 KB of stack, plus six String copies of
  // the memories and a String for the output, inside loopTask's 8 KB. The
  // page polls this every second, so the overflow presented as the board
  // rebooting at random rather than as anything pointing here.
  // 3072 since the Bluetooth block joined it.
  DynamicJsonDocument doc(3072);
  Settings::toJson(doc);
  JsonArray mems = doc.createNestedArray("mems");
  for (uint8_t i = 1; i <= Memories::COUNT; i++) mems.add(Memories::get(i));
  doc["call"] = Memories::call();
  doc["rssi"] = (int)WiFi.RSSI();
  doc["ip"]   = WiFi.localIP().toString();
  String out;
  out.reserve(1024);
  serializeJson(doc, out);
  server.send(200, "application/json", out);
}

void handleSet() {
  if (!server.hasArg("k") || !server.hasArg("v")) {
    server.send(400, "text/plain", "need k and v");
    return;
  }
  char msg[80];
  bool ok = Settings::apply(server.arg("k").c_str(), server.arg("v").c_str(),
                            msg, sizeof msg);
  Log::printf("[WEB] %s=%s -> %s\n", server.arg("k").c_str(),
                server.arg("v").c_str(), msg);
  server.send(ok ? 200 : 400, "text/plain", msg);
}

void handleSend() {
  // One button on the page is SEND or STOP depending on what is happening,
  // so the stop arrives on this endpoint. It has to clear the radio's buffer
  // too, not just the local one, and drop tune — the button is the only way
  // out of any of them now.
  if (server.hasArg("stop")) {
    HostLink::abort("clear: web STOP");
    Keyer::tune(false);
    Log::println("[WEB] stop");
    server.send(200, "text/plain", "stopped");
    return;
  }
  String t = server.arg("t");
  if (!t.length()) { server.send(400, "text/plain", "nothing to send"); return; }
  HostLink::sendText(t.c_str());
  Log::printf("[WEB] > %s\n", t.c_str());
  server.send(200, "text/plain", String("sent: ") + t);
}

void handleMem() {
  if (server.hasArg("call")) {
    Memories::setCall(server.arg("call").c_str());
    server.send(200, "text/plain", "callsign saved");
    return;
  }
  if (server.hasArg("play")) {
    uint8_t n = (uint8_t)server.arg("play").toInt();
    bool ok = Memories::play(n);
    server.send(ok ? 200 : 400, "text/plain",
                ok ? String("playing memory ") + n : String("memory is empty"));
    return;
  }
  uint8_t n = (uint8_t)server.arg("n").toInt();
  if (!Memories::set(n, server.arg("t").c_str())) {
    server.send(400, "text/plain", "bad slot, or over 100 characters");
    return;
  }
  server.send(200, "text/plain", String("memory ") + n + " saved");
}

void handleFsk() {
  if (server.hasArg("stop")) {
    Fsk::abort();
    server.send(200, "text/plain", "fsk stopped");
    return;
  }
  String t = server.arg("t");
  if (!t.length()) { server.send(400, "text/plain", "nothing to send"); return; }
  if (Keyer::practice()) {
    server.send(409, "text/plain", "practice mode: RTTY is not sent");
    return;
  }
  if (!Fsk::send(t.c_str())) {
    server.send(503, "text/plain", "fsk buffer full");
    return;
  }
  Log::printf("[FSK] > %s\n", t.c_str());
  server.send(200, "text/plain", String("fsk: ") + t);
}

// Radio finder. POST starts a sweep of one /24 for the SmartSDR API port;
// GET reports progress and what answered. Polled only while a scan runs,
// so it stays out of /api/state and that document's size budget.
void handleScanStart() {
  String net = server.arg("net");
  net.trim();
  if (Flex::scanRunning()) {
    server.send(409, "text/plain", "a scan is already running");
    return;
  }
  if (!Flex::scanStart(net.c_str())) {
    server.send(400, "text/plain", "subnet must be three octets, e.g. 192.168.1");
    return;
  }
  server.send(200, "text/plain",
              "scanning " + Flex::scanNet() + ".1-254 for a FlexRadio");
}

void handleScanState() {
  DynamicJsonDocument doc(768);
  doc["running"] = Flex::scanRunning();
  doc["tried"]   = Flex::scanTried();
  doc["net"]     = Flex::scanNet();
  doc["err"]     = Flex::scanError();
  JsonArray a = doc.createNestedArray("hits");
  Flex::ScanHit h[4];
  uint8_t n = Flex::scanHits(h, 4);
  for (uint8_t i = 0; i < n; i++) {
    JsonObject o = a.createNestedObject();
    o["ip"] = h[i].ip; o["model"] = h[i].model; o["name"] = h[i].name;
  }
  String out;
  serializeJson(doc, out);
  server.sendHeader("Cache-Control", "no-store");
  server.send(200, "application/json", out);
}

void handleBtState() {
  DynamicJsonDocument doc(1536);
  Bt::toJson(doc.to<JsonObject>(), true);
  String out;
  serializeJson(doc, out);
  server.sendHeader("Cache-Control", "no-store");
  server.send(200, "application/json", out);
}

void handleBtAction() {
  if (server.hasArg("restart")) {
    // A restart mid-over leaves a networked radio transmitting (it has
    // happened: interlock timeout=0), so not while anything is keyed.
    if (Keyer::busy() || Keyer::pttIsOn() || Flex::transmitting() || Fsk::busy()) {
      server.send(409, "text/plain", "not while transmitting — try again when it has finished");
      return;
    }
    server.send(200, "text/plain", "restarting — the page reconnects by itself");
    delay(300);
    ESP.restart();
  }
  if (!Bt::active()) {
    server.send(409, "text/plain", "bluetooth is not running — tick enabled, then RESTART");
    return;
  }
  if (server.hasArg("scan")) {
    bool ok = Bt::scanStart();
    server.send(ok ? 200 : 409, "text/plain",
                ok ? "scanning 10 s — keyboard in Bluetooth pairing mode"
                   : "busy connecting — try again in a moment");
    return;
  }
  if (server.hasArg("connect")) {
    bool ok = Bt::connect(server.arg("connect").c_str(), (uint8_t)server.arg("type").toInt());
    server.send(ok ? 200 : 400, "text/plain",
                ok ? "connecting — if a passkey appears, type it on the keyboard"
                   : "bad address");
    return;
  }
  if (server.hasArg("forget")) {
    Bt::forget();
    server.send(200, "text/plain", "keyboard forgotten");
    return;
  }
  server.send(400, "text/plain", "need scan, connect, forget or restart");
}

void handleTune() {
  bool on = server.arg("v") == "on";
  Keyer::tune(on);
  server.send(200, "text/plain", on ? "tune on — key down" : "tune off");
}

}  // namespace

namespace Web {

void begin() {
  server.on("/", HTTP_GET, []() {
    // The page is baked into the firmware and changes on almost every
    // flash, so a cached copy is always the wrong one. Served with no
    // headers at all it could be held indefinitely.
    server.sendHeader("Cache-Control", "no-store, must-revalidate");
    server.send_P(200, "text/html", PAGE);
  });
  server.on("/api/state", HTTP_GET,  handleState);
  // Host traffic trace — ?clear=1 empties it. Kept off /api/state, which the
  // page polls every second.
  server.on("/api/wktrace", HTTP_GET, []() {
    if (server.hasArg("clear")) {
      HostLink::traceClear();
      server.send(200, "text/plain", "cleared\n");
      return;
    }
    String out;
    HostLink::traceDump(out);
    server.send(200, "text/plain", out);
  });
  // Radio traffic trace — ?clear=1 empties it. Streamed in chunks: the full
  // ring is ~15 KB of text, too much to build as one String on this heap.
  server.on("/api/flextrace", HTTP_GET, []() {
    if (server.hasArg("clear")) {
      Flex::traceClear();
      server.send(200, "text/plain", "cleared\n");
      return;
    }
    struct Chunked : Print {
      char buf[1024]; size_t n = 0;
      size_t write(uint8_t c) override {
        buf[n++] = (char)c;
        if (n == sizeof buf) flush();
        return 1;
      }
      void flush() override { if (n) server.sendContent(buf, n); n = 0; }
    } out;
    server.setContentLength(CONTENT_LENGTH_UNKNOWN);
    server.send(200, "text/plain", "");
    Flex::traceDump(out);
    out.flush();
    server.sendContent("");
  });
  // Radio CW timing table (5-50 WPM). ?reset=1 (POST) forgets it.
  server.on("/api/cwtable", HTTP_GET, []() {
    DynamicJsonDocument doc(4096);          // 46 x {wpm, us, runs}
    Flex::cwTableJson(doc.createNestedArray("table"));
    String out;
    serializeJson(doc, out);
    server.send(200, "application/json", out);
  });
  server.on("/api/cwtable", HTTP_POST, []() {
    if (server.hasArg("reset")) { Flex::cwTableReset(); server.send(200, "text/plain", "cw table reset\n"); return; }
    server.send(400, "text/plain", "need reset=1\n");
  });
  server.on("/api/set",   HTTP_POST, handleSet);
  server.on("/api/send",  HTTP_POST, handleSend);
  server.on("/api/tune",  HTTP_POST, handleTune);
  server.on("/api/fsk",   HTTP_POST, handleFsk);
  server.on("/api/mem",   HTTP_POST, handleMem);
  server.on("/api/flexscan", HTTP_POST, handleScanStart);
  server.on("/api/flexscan", HTTP_GET,  handleScanState);
  server.on("/api/bt", HTTP_GET,  handleBtState);
  server.on("/api/bt", HTTP_POST, handleBtAction);
  server.onNotFound([]() { server.send(404, "text/plain", "no such page"); });
  // Listening is deferred to poll(): WiFiManager is non-blocking, so at
  // setup() time there is usually no IP to bind to yet. Net::poll() brings
  // mDNS up on the same transition and registers the http service there.
}

void poll() {
  if (WiFi.status() != WL_CONNECTED) {
    if (started) { server.stop(); started = false; }
    return;
  }
  if (!started) {
    server.begin();
    started = true;
    Log::printf("[WEB] settings at http://%s.local/ or http://%s/\n",
                  MDNS_HOSTNAME, WiFi.localIP().toString().c_str());
  }
  server.handleClient();
}

}  // namespace Web
