vu2cpl/esp32-winkeyer/include/flex.h

#pragma once

// ============================================================
//  VUKEYER — FlexRadio (SmartSDR) backend
//
//  Finds a 6000/8000-series radio on the LAN via its discovery
//  broadcast, opens the SmartSDR command API on TCP 4992, and
//  keys CW with "cwx send" — the radio generates the element
//  timing, so network jitter never reaches the air.
// ============================================================

#include <Arduino.h>
#include <ArduinoJson.h>

namespace Flex {

void begin();
void poll();

void setEnabled(bool on);      // persisted in NVS
bool enabled();
bool connected();

void   setManualIp(const char* ip);   // "" = use discovery
String manualIp();
String radioIp();
String radioModel();

// Real-time keying. keyEvent() is safe to call from the keyer task; it only
// queues, and poll() does the network write.
void keyEvent(bool down);
void setDirectKeying(bool on);
bool directKeying();

// How long to hold the transmitter after the last element before "xmit 0".
// This is the Flex path's own tail, and it is a SEPARATE transmitter from
// the keyer's: the keyer's tail releases the local PTT line (GPIO32, still
// live on this backend for an amp or sequencer), this one releases the
// radio. Both must be set together or the control silently does nothing to
// whichever one you are listening to. Settings::apply() keeps them in step.
void     setPttTailMs(uint16_t ms);
uint16_t pttTailMs();

// True while we are holding the radio's transmitter (xmit 1 sent, xmit 0
// not yet). Distinct from the local PTT line, which is the keyer's.
bool     transmitting();

// Whether to assert PTT (xmit 1) around keying. With break-in/QSK the
// radio can switch T/R off the key edge alone, in which case asserting
// PTT ourselves may suppress the carrier. Runtime-switchable so this can
// be settled by ear rather than by reflashing.
void setUseXmit(bool on);
bool useXmit();

// Whether to issue "client bind" to the GUI client. Default OFF: binding to a
// GUI client that had just connected wedged the radio's CW generator, and
// paddle keying and CWX both went out at 0 W (HANDOVER item 13). The radio
// keys fine unbound. Kept switchable so that can be tested again.
void setBind(bool on);
bool bindEnabled();

// Handle of the GUI client every cw key is sent on behalf of, e.g.
// "0x3CF2DCF6"; "" until one is seen. Followed across that client leaving,
// restarting under a new handle, and our own reconnect.
String guiClientHandle();

// Last 128 lines to and from the radio with millisecond stamps: every
// command sent, and the replies, messages and interlock/cwx/client statuses
// received. Served at GET /api/flextrace (?clear=1 empties it).
void traceDump(Print& out);
void traceClear();

// "ptt" (FlexRadio wiki) or "key" (MORCONI). Both are accepted by the
// radio; only a power meter can say which one keys.
void        setKeyVerb(const char* verb);
const char* keyVerb();

// True when the radio has a slice in use and in CW mode. Without both the
// radio transmits nothing and reports no error at all.
bool sliceReady();

// Measured delay between handing the radio text and it starting to
// transmit — the network hop plus the radio's own CW start. 0 until a
// transmission has been timed. Used to align the local sidetone copy.
uint16_t startLatencyMs();

// How much longer than 1200/WPM the radio makes each dit unit of CWX, in µs,
// at this speed: learned per speed from its "cwx sent=" reports, interpolated
// between learned speeds, 700 until any are. Kept in NVS. The sidetone copy of
// radio-generated text adds it.
int16_t cwExtraUs(uint8_t wpm);
void    cwTableJson(JsonArray a);    // [{wpm, us, runs}] for 5..50 WPM
void    cwTableReset();              // forget everything learned (and the start delay)

// Operator-facing reason the radio will not transmit CW, or "" when it
// will (or when not connected — that has its own indicator). Caller's
// buffer, as the display task and the web handler run on different cores.
enum WarnForm : uint8_t {
  WARN_LONG,    // web page sentence
  WARN_SHORT,   // <= 18 chars: OLED title, 20x4 LCD row
  WARN_TINY,    // <= 16 chars: 16x2 LCD row
};
void sliceWarning(char* out, size_t n, WarnForm form);

// LAN scan. Discovery is a UDP broadcast and never leaves the keyer's own
// subnet, so a radio on another segment is invisible to it. The command API
// is plain TCP, which a router forwards like anything else: scanStart()
// sweeps one /24 for port 4992 in a background task and asks whatever
// answers what it is. Read-only on the radio — it opens a connection,
// reads the greeting, asks "info", and closes.
struct ScanHit {
  char ip[16];
  char model[24];
  char name[32];     // radio nickname, else callsign
};
bool    scanStart(const char* prefix);   // "192.168.1"; "" = keyer's own /24
bool    scanRunning();
uint8_t scanTried();                     // hosts done, 0..254
String  scanNet();                       // the /24 being / last scanned
String  scanError();                     // "" unless the sweep gave up
uint8_t scanHits(ScanHit* out, uint8_t max);

void send(const char* text);   // queue text for transmission (cwx send)
// cwx clear. `why` goes into /api/flextrace as a "#" line just before it, so
// a message cut short can be traced to what stopped it.
void clear(const char* why);
void setWpm(uint8_t wpm);      // cwx wpm
uint8_t radioWpm();            // cwx speed the RADIO last reported, 0 = unknown
bool radioTransmitting();      // interlock state=TRANSMITTING, any source
int  pending();                // characters queued but not yet keyed

}  // namespace Flex
