vu2cpl/esp32-winkeyer/include/memories.h

#pragma once

// ============================================================
//  VUKEYER — message memories
//
//  Six slots of canned text in NVS, played through whichever
//  backend is current. No GPIO cost: they are triggered from the
//  web page, the CLI or the host, and front-panel buttons can be
//  wired to them later without changing any of this.
//
//  %C expands to your callsign so the same memory works when the
//  call changes for a contest or a portable operation.
// ============================================================

#include <Arduino.h>

namespace Memories {

static const uint8_t COUNT   = 6;
static const size_t  MAX_LEN = 100;

void   begin();
bool   set(uint8_t slot, const char* text);   // 1..COUNT; "" clears
String get(uint8_t slot);
bool   play(uint8_t slot);                    // false if empty or out of range
// Which slot is playing right now, 0 for none. The page turns that row's
// PLAY into STOP, so it has to be the slot itself and not just "busy" —
// six STOP buttons, or one on the wrong row, is worse than none.
uint8_t playing();

void   setCall(const char* call);
String call();

}  // namespace Memories
